leonvandenbeukel/Wi-Fi-Audio-Control/Server/Equalizer.h

/*
  I've used the Fixed Point Table Generator (Menu Tools) in SigmaStudio, generated .hz file for each freq. and converted to 1 file 
  with a c# tool and copied to this file
  
  The Tab Peaking - Low - High Shelf is used, settings:
  Boost min: -10, Boost Max: 10, Number of Steps: 21 (-10 to +10 and mind the 0 also counts)
  Frequencies: 100, 500, 1000, 2000, 5000, 8000
  Q: 1.41
  Change Peaking, High Shelf and Low Shelf according to the settings of the frequency settings (click little symbol on top of the eq)

  When 'Show values' is checked and click 'Generate' you can see something like this:

    Boost=-10
    b0=0.992906451225281,  0x00 ,  0x7F ,  0x17 ,  0x8F ,  
    b1=-1.96762752532959, 0xFF ,  0x04 ,  0x24 ,  0xC8 ,  
    b2=0.974833488464355, 0x00 ,  0x7C ,  0xC7 ,  0x58 ,  
    a1=1.96750617027283,  0x00 ,  0xFB ,  0xD7 ,  0x3E ,  
    a2=-0.967861294746399,  0xFF ,  0x84 ,  0x1D ,  0x1F ,  
    ...
    
  Uncheck 'Show values' and click generate (6x).

 */

/*
 * 10 = nr of bands
 * 49 = nr of values from min to max of each eq band
 * 5  = there are 5 registers that has to be set (B0, B1, B2, A1, A2)
 * 4  = 4 bytes has to be set to every register
 */

byte bands[10][49][5][4] = 
{
  {
    {
      { 0x00 ,  0x7F ,  0xC4 ,  0x8E },
      { 0xFF ,  0x00 ,  0xEE ,  0x2E },
      { 0x00 ,  0x7F ,  0x4D ,  0x9B },
      { 0x00 ,  0xFF ,  0x11 ,  0x50 },
      { 0xFF ,  0x80 ,  0xED ,  0x56 },
    },{
      { 0x00 ,  0x7F ,  0xC6 ,  0xDA },
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
      { 0xFF ,  0xC0 ,  0xA0 ,  0xFE },
    },{
      { 0x00 ,  0xBB ,  0x36 ,  0x70 },
      { 0x00 ,  0x64 ,  0x72 ,  0xF7 },
      { 0x00 ,  0x3B ,  0xD5 ,  0x08 },
      { 0xFF ,  0x64 ,  0xAA ,  0x27 },
      { 0xFF ,  0xBF ,  0xD7 ,  0x6B },
    }
  }
};
